sdp8483/Joule_Candle/images/2017-11-28 14.42.37.jpg

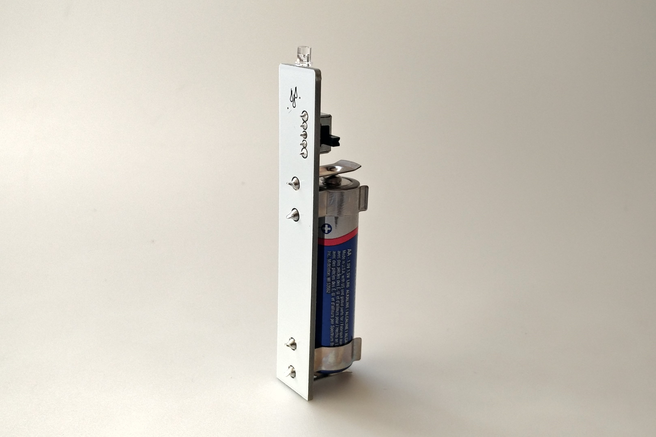
images/2017-11-28 14.42.37.jpg
