sdp8483/Joule_Candle/assembly/3d_printed_tooling/images/led_lead_cutting_guide.png

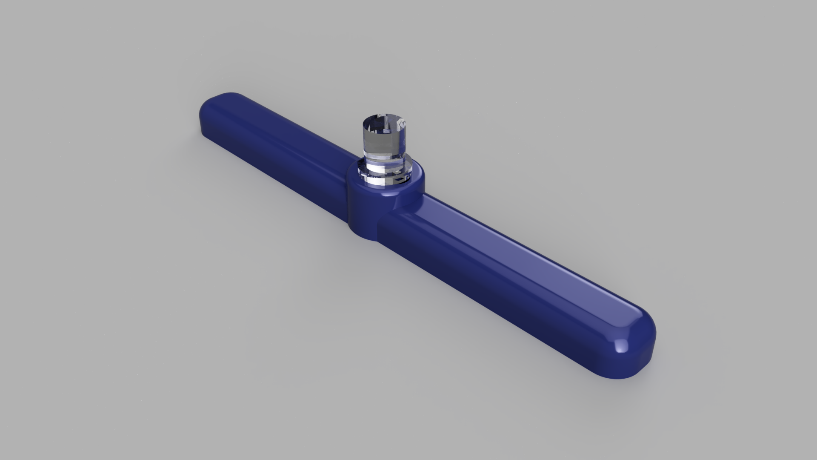
assembly/3d_printed_tooling/images/led_lead_cutting_guide.png
