sdp8483/Joule_Candle/assembly/3d_printed_tooling/images/led_solder_jig.png

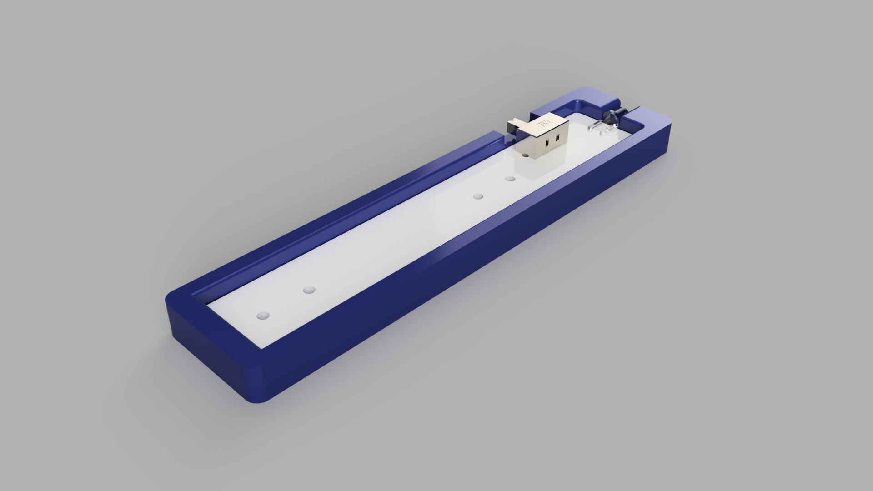
assembly/3d_printed_tooling/images/led_solder_jig.png
