sdp8483/Joule_Candle/assembly/3d_printed_tooling/images/modified_vise_jaws.png

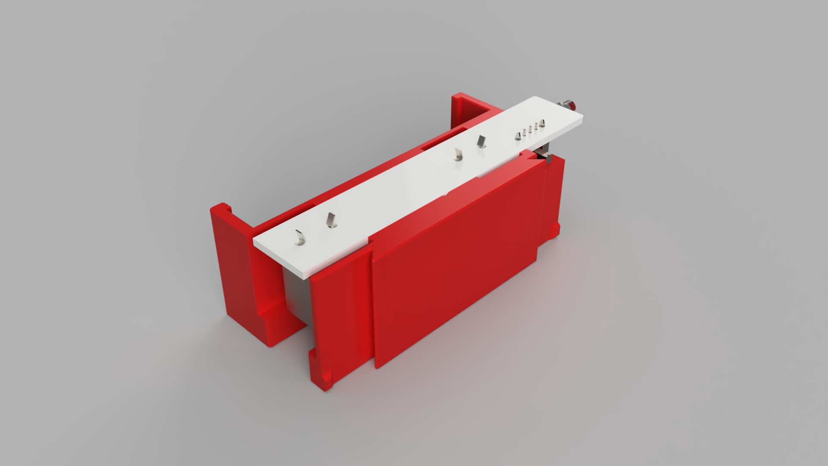
assembly/3d_printed_tooling/images/modified_vise_jaws.png
